serdzz/rp2350-sim800l-ppp/src/config.rs

//! Всё, что нужно править под свою плату / оператора — собрано здесь.

use crate::coin;

/// APN оператора. Примеры: "internet" (МТС/Билайн), "internet.tele2.ru",
/// "internet.beeline.ru", "iot.1nce.net".
pub const APN: &str = "internet";

/// Логин/пароль PAP для PPP. У большинства российских операторов пустые;
/// у Билайна исторически "beeline"/"beeline", у МТС "mts"/"mts".
pub const PPP_USERNAME: &[u8] = b"";
pub const PPP_PASSWORD: &[u8] = b"";

/// Строка дозвона в PPP-режим. `*99***1#` использует PDP-контекст №1,
/// который мы настраиваем через AT+CGDCONT. Некоторые прошивки понимают
/// только короткое `*99#`.
pub const DIAL_STRING: &str = "*99***1#";

/// Скорость UART модема. SIM800L автоопределяет скорость по первым "AT",
/// но для PPP её нужно зафиксировать — см. `modem::SetBaudRate`.
pub const UART_BAUDRATE: u32 = 115_200;

/// Сколько ждать регистрации в сети (шаг опроса — 2 с).
pub const REGISTRATION_ATTEMPTS: u32 = 60;

/// Запускать `AT+COPS=?` (поиск всех видимых сетей), если регистрация не
/// удалась. Команда занимает до нескольких минут и удлиняет цикл повтора,
/// зато прямо отвечает, виден ли вообще 2G. Для отладки — да, в поле — нет.
pub const SCAN_OPERATORS_ON_FAILURE: bool = true;

/// Считать `Call Ready` / `SMS Ready` признаком перезагрузки модуля.
///
/// Ловит почти все сбросы по питанию, тогда как один только `RDY` — примерно
/// каждый пятый. Плата за это — один лишний цикл инициализации при первом
/// подключении: те же URC модуль шлёт и при нормальном старте. Для отладки
/// питания — да, в отлаженном устройстве можно выключить.
pub const TREAT_READY_URCS_AS_RESET: bool = true;

// --- CMUX (ветка feat/cmux) ---

/// Поднимать канал через мультиплексор 27.010 вместо передачи UART из рук
/// в руки.
///
/// Включено на ветке feat/cmux для проверки на стенде. Если мультиплексор
/// не поднимется, вернуть `false` — путь без него проверен и доходит до
/// HTTP 200.
pub const USE_CMUX: bool = true;

/// Канал под AT-команды в мультиплексном режиме.
pub const CMUX_AT_DLCI: u8 = 1;
/// Канал под PPP.
pub const CMUX_PPP_DLCI: u8 = 2;
/// N1 из `AT+CMUX` — максимум байт в поле данных кадра.
///
/// 127 держит поле длины однооктетным; PPP при этом просто разложит свои
/// кадры на несколько UIH.
pub const CMUX_MAX_PAYLOAD: u16 = 127;
/// Сколько раз повторить SABM, если модем промолчал.
pub const CMUX_OPEN_ATTEMPTS: u32 = 5;

/// Пауза перед повторной попыткой после развала PPP-сессии.
pub const RECONNECT_DELAY_SECS: u64 = 10;

// --- MQTT ---

/// Брокер. Публичный тестовый: подключается без учётных данных, удобно для
/// проверки. Для чего-то настоящего поставьте свой.
///
/// Не `test.mosquitto.org`: он регулярно лежит, и на стенде мы получили от
/// него RST на каждой попытке — причём он был недоступен и с обычного
/// интернета, то есть дело не в GPRS.
pub const MQTT_HOST: &str = "broker.hivemq.com";
pub const MQTT_PORT: u16 = 1883;
/// Идентификатор клиента — должен быть уникален в пределах брокера.
pub const MQTT_CLIENT_ID: &str = "rp2350-sim800l";
/// Топик для уровня сигнала (публикуем).
pub const MQTT_TOPIC_CSQ: &str = "rp2350-sim800l/csq";
// --- Монетоприёмник NRI G-13 mft ---

/// Монеты и коды, которыми приёмник о них сообщает.
///
/// Код — состояние всех шести линий, снятое разом. Однобитный код означает
/// «одна монета на линию», многобитный — двоичное кодирование, которое
/// документация допускает прямо («possible to transmit coin signals in a binary
/// code or assign more than one line to a type of coin»).
///
/// # Почему монет вдвое больше, чем на самом деле
///
/// Столбец на шильдике со значениями 1…6 читается двояко, и однозначно его
/// решает только монета:
///
/// * **номер линии** — тогда 1 евро это линия 5, то есть `0b010000`;
/// * **двоичный код** — тогда 1 евро это пины 1+3, то есть `0b000101`.
///
/// Рабочий автомат на MSP430 (`bahilizator_kwt_svn`) устроен по первому
/// варианту: там шесть каналов, по монете на каждый, а номиналы оператор
/// вводит с экрана. Но это другой экземпляр приёмника, и настроен он мог быть
/// иначе.
///
/// Поэтому здесь перечислены **оба** кода. Столкнуться они не могут: при
/// однобитной раскладке `0b000101` не появится никогда (две линии разом не
/// зажигаются), при двоичной — не появится `0b010000` (кода 16 на шильдике
/// нет). Так что ошибиться нельзя, а лог сразу скажет, какой вариант ваш:
///
/// ```text
/// COIN: EUR 1 (линия 5) (код 0b010000), номинал 100, кредит 100
/// ```
///
/// Увидели — лишнюю строку отсюда удалите.
///
/// # Если код окажется третьим
///
/// Неизвестный код печатается готовым к вписыванию:
///
/// ```text
/// COIN: неизвестный код 0b000101 — впишите его в config::COINS
/// ```
///
/// # Что не считаем
///
/// Лат, рубль и гривна в таблице отсутствуют намеренно: лат выведен из
/// обращения в 2014-м, остальное — чужая валюта. Их коды прошивка напечатает
/// и кредита не даст. Физически глушить их надо переключателями на корпусе —
/// см. [`COIN_BLOCK_DEFAULT`].
///
/// Жетоны различить нельзя: все пять их каналов дают один код. Значение 100 —
/// предположение «жетон равен одному евро»; поставьте своё.
pub const COINS: &[coin::Coin] = &[
    coin::Coin {
        mask: 0b010000,
        value: 100,
        name: "EUR 1 (линия 5)",
    },
    coin::Coin {
        mask: 0b000101,
        value: 100,
        name: "EUR 1 (код 5)",
    },
    coin::Coin {
        mask: 0b100000,
        value: 100,
        name: "жетон (линия 6)",
    },
    coin::Coin {
        mask: 0b000110,
        value: 100,
        name: "жетон (код 6)",
    },
];

/// Какие линии заблокированы сразу после старта. Бит 0 — линия 1.
///
/// Ноль, и это осознанно. При двоичном кодировании закрыть **монету** линиями
/// невозможно: пин 1 участвует и в лате (`1`), и в гривне (`3`), и в евро
/// (`5`), так что блокировка линии калечит чужие коды, а не отсекает лишнее.
///
/// Ненужные монеты глушатся не отсюда, а переключателями на корпусе приёмника:
/// там это делается по каналам, поштучно и надёжно. `S1.1…8` — каналы 1–8,
/// `S2.1…8` — каналы 9–16. Лат, например, занимает каналы 01 и 06, значит
/// выключить надо оба.
///
/// Команда [`MQTT_TOPIC_COIN_BLOCK`] остаётся: она управляет линиями как есть,
/// и на приёмнике с одной монетой на линию работает ожидаемо.
pub const COIN_BLOCK_DEFAULT: u8 = 0;

/// Топик событий монетоприёмника (публикуем).
pub const MQTT_TOPIC_COIN: &str = "rp2350-sim800l/coin";

/// Инвертирует ли буферный каскад сигнал полной блокировки на `GP9`.
///
/// Вход `total blocking` приёмника (контакт 6) активен **высоким**: блокировка
/// при `≥ 3.5 В`, приём при `≤ 1 В`. Плата выдаёт 3.3 В, то есть под порогом,
/// поэтому напрямую вывод сюда заводить нельзя.
///
/// `false` — проверенная схема: BSS138 как на линиях, плюс подтяжка стока к
/// `+5 В` (в рабочем автомате это `Q5` и `R45` 10 кОм). Такой каскад **не
/// инвертирует**: `GP9` высокий → полевик закрыт → линия подтянута к 5 В →
/// блокировка.
///
/// К этой схеме обязателен резистор 10 кОм от `GP9` к `+3.3 В`. Без него вывод
/// в сбросе не управляется, линия уходит к нулю, и мёртвый автомат принимает
/// монеты, не давая кредита. С подтяжкой неуправляемый вывод означает
/// «заблокировано» — то есть безопасное состояние совпадает с неуправляемым.
///
/// `true` — если собран инвертирующий каскад, например NPN с подтяжкой
/// коллектора к +12 В.
pub const COIN_TOTAL_BLOCK_INVERTED: bool = false;

/// Топик полной блокировки приёмника (подписываемся). Тело: `block`/`accept`.
pub const MQTT_TOPIC_COIN_TOTAL: &str = "rp2350-sim800l/coin/total";

/// Топик блокировки каналов монетоприёмника (подписываемся).
///
/// Тело — список номеров линий: `none`, `all`, `1,3`. Разбор — в
/// [`crate::coin::parse_block_mask`].
pub const MQTT_TOPIC_COIN_BLOCK: &str = "rp2350-sim800l/coin/block";

/// Топик для принятых SMS (публикуем).
pub const MQTT_TOPIC_SMS: &str = "rp2350-sim800l/sms";

/// Префикс топика отправки SMS (подписываемся).
///
/// Номер идёт последним сегментом топика, текст — телом сообщения:
/// `rp2350-sim800l/sms/send/37120000000`.
///
/// **Номер только цифрами, без плюса.** В имени топика MQTT плюс запрещён —
/// это подстановочный знак, — и брокер такую публикацию отвергнет. Плюс
/// подставляется прошивкой перед отправкой.
pub const MQTT_TOPIC_SMS_SEND: &str = "rp2350-sim800l/sms/send/";

/// Подписка на отправку: последний сегмент — любой.
pub const MQTT_TOPIC_SMS_SEND_FILTER: &str = "rp2350-sim800l/sms/send/+";
/// Топик управления светодиодом (подписываемся).
///
/// Тело: `ON`, `OFF`, `BLINK` или `TOGGLE`. Первые три задают состояние,
/// последняя зависит от текущего — см. [`crate::led::toggle`].
pub const MQTT_TOPIC_LED: &str = "rp2350-sim800l/led";
/// Как часто публиковать CSQ.
pub const MQTT_PUBLISH_SECS: u64 = 60;

/// Хост для демо-запроса после подъёма IP.
pub const DEMO_HOST: &str = "example.com";
pub const DEMO_PORT: u16 = 80;
