serdzz/rp2350-sim800l-ppp/src/fuel.rs

//! Топливомер MAX17048 (SparkFun Qwiic Fuel Gauge) на общей шине I2C.
//!
//! ```text
//!   RP2350            Qwiic
//!   GP16 ── SDA ──┬── MAX17048 (0x36)
//!   GP17 ── SCL ──┤
//!   3V3  ── VCC ──┤   и SSD1306 (0x3C) на той же шине
//!   GND  ── GND ──┘
//! ```
//!
//! Аккумулятор подключается к самому топливомеру, а не к плате: он меряет
//! напряжение прямо на банке.
//!
//! # Зачем он, если есть `battery.rs`
//!
//! Затем, что тот меряет не банку, а VSYS, и при воткнутом USB о батарее не
//! говорит ничего: VBUS через диод задаёт VSYS независимо от её состояния.
//! Мы на это уже натыкались — «батарея не измеряется» в каждой строке лога.
//!
//! MAX17048 такого ограничения не имеет. Заодно он считает заряд не по
//! напряжению, а по своей модели разряда: под нагрузкой напряжение проседает,
//! и пересчёт «вольты → проценты» врёт тем сильнее, чем больше ток. У модема
//! этот ток доходит до двух ампер.
//!
//! # Про общую шину
//!
//! Экран работает с шиной асинхронно, а `max170xx` — блокирующий крейт. Свести
//! их удалось потому, что `embassy_rp::I2c` реализует оба трейта сразу: экран
//! ходит через асинхронную обёртку, а здесь мы берём мьютекс и обращаемся к
//! шине напрямую. Транзакция короткая — пара байт, — так что блокировка внутри
//! асинхронной задачи здесь безобидна.

use core::sync::atomic::{AtomicU16, Ordering};

use embassy_rp::i2c::{Async, I2c};
use embassy_rp::peripherals::I2C0;
use embassy_sync::blocking_mutex::raw::CriticalSectionRawMutex;
use embassy_sync::mutex::Mutex;
use embassy_time::{Duration, Timer, with_timeout};
use max170xx::Max17048;

/// Шина, разделяемая экраном и топливомером.
pub type I2cBus = Mutex<CriticalSectionRawMutex, I2c<'static, I2C0, Async>>;

/// Как часто опрашивать. Заряд меняется медленно, чаще незачем.
const POLL: Duration = Duration::from_secs(10);

/// Адрес MAX17048 на шине. Крейт держит его внутри, а нам он нужен для
/// проверки присутствия — см. [`fuel_task`].
const ADDRESS: u8 = 0x36;

/// Регистр версии: читать его безобидно, а записать один байт указателя —
/// самая короткая транзакция, какой можно спросить «ты здесь?».
const VERSION_REG: u8 = 0x08;

/// Сколько ждать отклика на проверку присутствия.
///
/// Байт на 100 кГц уходит за сотню микросекунд, так что сто миллисекунд — это
/// с тысячекратным запасом и всё равно незаметно.
const PROBE_TIMEOUT: Duration = Duration::from_millis(100);

/// Признак «показаний нет».
///
/// Ноль не годится: разряженная в ноль банка — вполне возможное показание, и
/// спутать его с отсутствующим датчиком нельзя.
const NO_READING: u16 = u16::MAX;

/// Напряжение наружу не отдаётся: показывать его негде, а в лог оно уходит
/// там же, где читается. Держим отдельным полем только затем, чтобы не
/// печатать устаревшее значение при потере датчика.
static PERMILLE: AtomicU16 = AtomicU16::new(NO_READING);

/// Заряд в промилле (0…1000). `None`, если топливомера нет.
///
/// Промилле, а не проценты: датчик отдаёт дробное значение, и округлять его до
/// целых процентов прямо при чтении — терять то, что он посчитал.
pub fn permille() -> Option<u16> {
    match PERMILLE.load(Ordering::Relaxed) {
        NO_READING => None,
        pm => Some(pm),
    }
}

/// Заряд в процентах, для показа человеку.
pub fn percent() -> Option<u8> {
    permille().map(|pm| ((pm + 5) / 10).min(100) as u8)
}

/// Опрашивает топливомер и складывает показания в атомики.
#[embassy_executor::task]
pub async fn fuel_task(bus: &'static I2cBus) -> ! {
    // `None` до первого опроса. Три состояния, а не два, потому что молчание
    // датчика с самого включения — тоже новость, и о ней надо сказать. Флаг
    // из двух состояний её проглатывал: не отвечал — значит и «перестал
    // отвечать» печатать не о чем, и в логе не было ни строчки.
    let mut answering: Option<bool> = None;

    loop {
        // Мьютекс держим только на время обмена: экран рисует раз в секунду и
        // ждать нас не должен.
        let reading = {
            let mut i2c = bus.lock().await;

            // Сперва спрашиваем шину асинхронно и с таймаутом, и только потом
            // отдаём её блокирующему крейту.
            //
            // Порядок именно такой не из аккуратности: блокирующий вызов
            // нечем прервать. На залипшей шине он вешает задачу навсегда, а
            // вместе с ней и мьютекс — то есть заодно и экран, которому эта
            // шина тоже нужна. Проверка присутствия ограничивает риск: до
            // блокирующего вызова дело доходит, только если устройство
            // ответило.
            let present = with_timeout(
                PROBE_TIMEOUT,
                embedded_hal_async::i2c::I2c::write(&mut *i2c, ADDRESS, &[VERSION_REG]),
            )
            .await;

            match present {
                Ok(Ok(())) => {
                    let mut gauge = Max17048::new(&mut *i2c);
                    match (gauge.voltage(), gauge.soc()) {
                        (Ok(v), Ok(soc)) => Some((v, soc)),
                        _ => None,
                    }
                }
                _ => None,
            }
        };

        match reading {
            Some((volts, soc)) => {
                if answering != Some(true) {
                    info!("FUEL: MAX17048 отвечает");
                    answering = Some(true);
                }
                PERMILLE.store((soc * 10.0).clamp(0.0, 1000.0) as u16, Ordering::Relaxed);
                info!(
                    "FUEL: батарея {} мВ, заряд {} %",
                    (volts * 1000.0) as u16,
                    (soc + 0.5) as u16
                );
            }
            None => {
                // Показание стираем, а не оставляем последнее: устаревшие
                // проценты на экране хуже честного прочерка.
                PERMILLE.store(NO_READING, Ordering::Relaxed);
                match answering {
                    None => warn!(
                        "FUEL: MAX17048 не отвечает по адресу 0x36 — подключён ли к GP16/GP17?"
                    ),
                    Some(true) => warn!("FUEL: MAX17048 перестал отвечать"),
                    Some(false) => {}
                }
                answering = Some(false);
            }
        }

        Timer::after(POLL).await;
    }
}
